DoESLiverpool/st-johns-beacon/large-multi-piece/RCT - Top Windows.stl

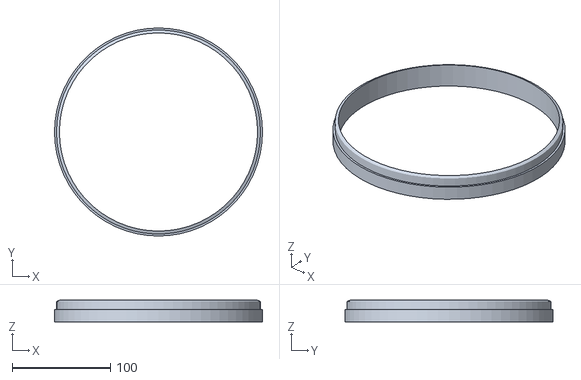
[picture p15: CAD file, 2015-06-18]
large-multi-piece/RCT - Top Windows.stl
211.2 x 211.2 x 22.1
