DoESLiverpool/st-johns-beacon/small-five-piece/St John's Beacon, Radio City Tower - Tower Base 1.stl

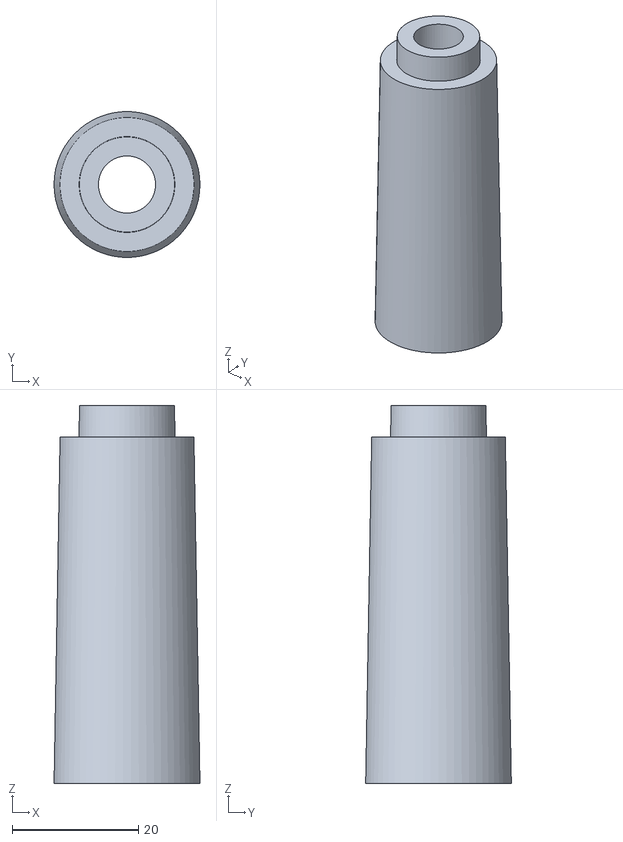
[picture p16: CAD file, 2015-06-10]
small-five-piece/St John's Beacon, Radio City Tower - Tower Base 1.stl
23.2 x 23.1 x 60.0
