DoESLiverpool/st-johns-beacon/large-multi-piece/Letter Ring/letter-i.stl

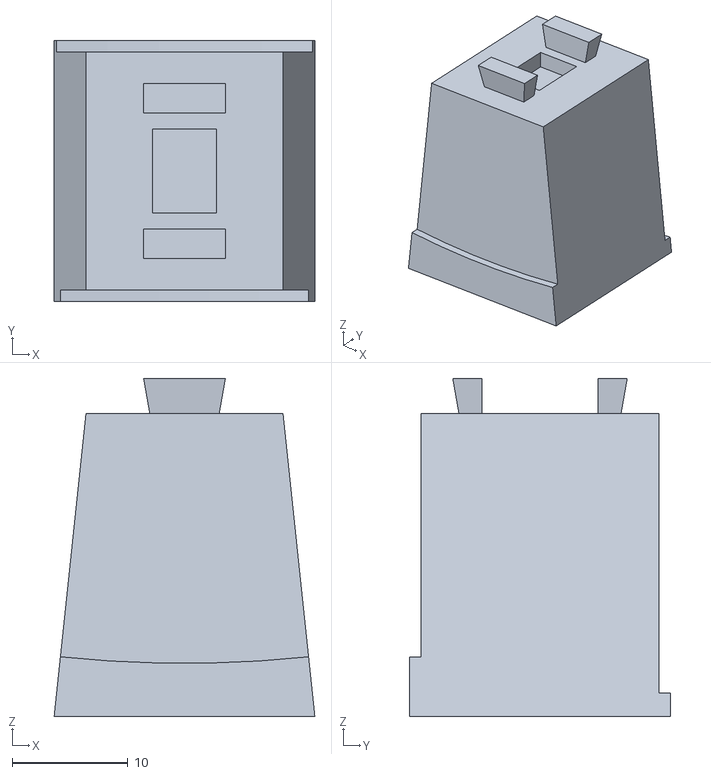
[picture p17: CAD file, 2015-06-19]
large-multi-piece/Letter Ring/letter-i.stl
22.5 x 22.5 x 29.2
