DoESLiverpool/st-johns-beacon/large-multi-piece/RCT - Letter block ring.stl

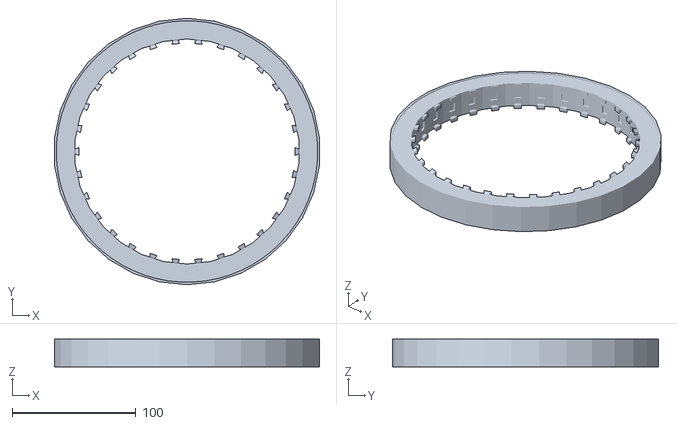
[picture p18: CAD file, 2015-06-18]
large-multi-piece/RCT - Letter block ring.stl
214.1 x 215.3 x 22.5
