DoESLiverpool/st-johns-beacon/small-five-piece/St John's Beacon, Radio City Tower - Tower Base 3.stl

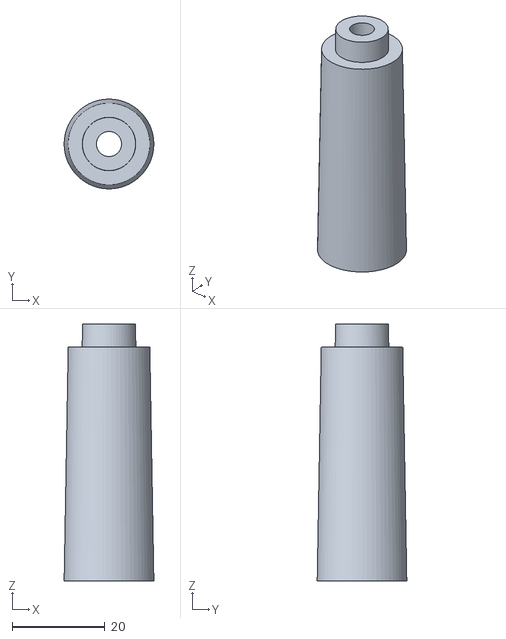
[picture p19: CAD file, 2015-06-10]
small-five-piece/St John's Beacon, Radio City Tower - Tower Base 3.stl
19.3 x 19.3 x 55.3
