DoESLiverpool/st-johns-beacon/large-multi-piece/Letter Ring/letter-S.stl

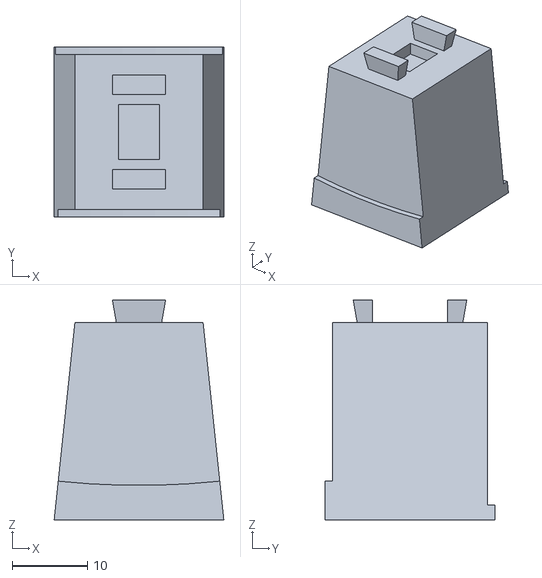
[picture p20: CAD file, 2015-06-19]
large-multi-piece/Letter Ring/letter-S.stl
22.5 x 22.5 x 29.2
