DoESLiverpool/st-johns-beacon/large-multi-piece/RCT - Chimney.stl

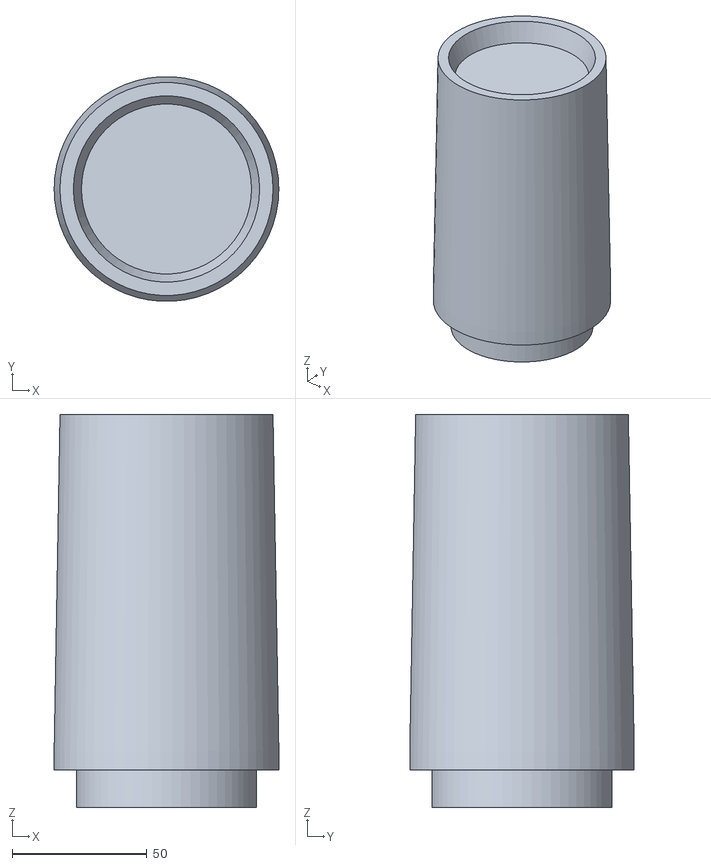
[picture p21: CAD file, 2015-06-15]
large-multi-piece/RCT - Chimney.stl
83.6 x 83.4 x 146.1
