DoESLiverpool/st-johns-beacon/large-multi-piece/RCT - Roof.stl

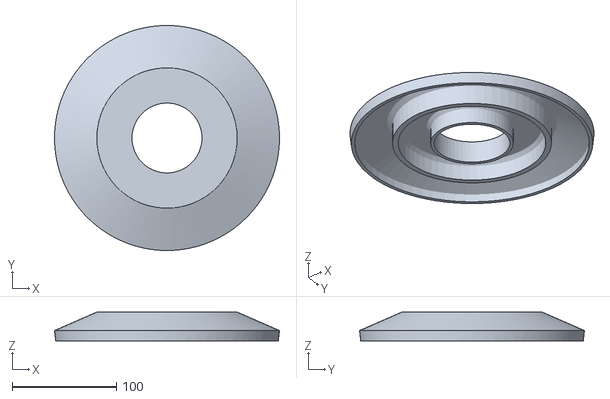
[picture p22: CAD file, 2015-06-15]
large-multi-piece/RCT - Roof.stl
215.5 x 215.4 x 27.6
