DoESLiverpool/st-johns-beacon/large-multi-piece/RCT - Tower Base 2.stl

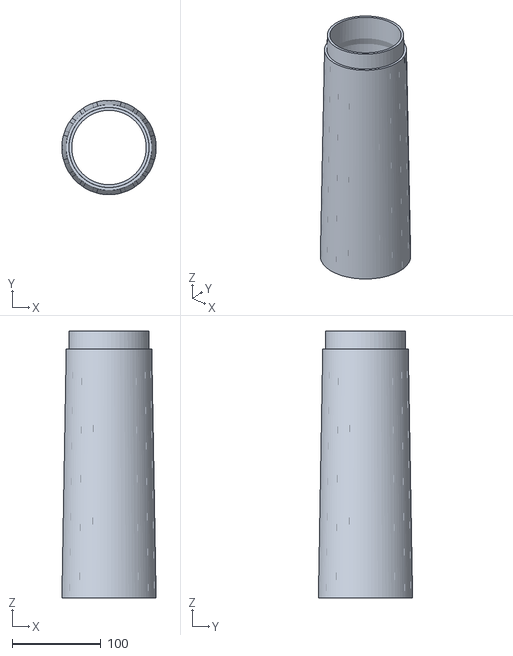
[picture p23: CAD file, 2015-06-15]
large-multi-piece/RCT - Tower Base 2.stl
105.9 x 105.9 x 300.0
