DoESLiverpool/st-johns-beacon/large-multi-piece/RCT - Tower Base 3.stl

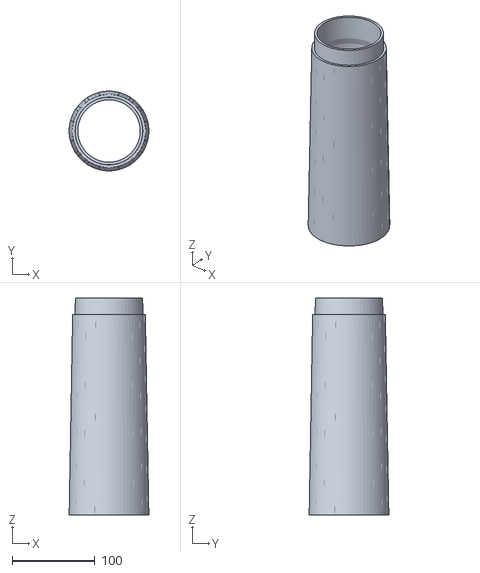
[picture p24: CAD file, 2015-06-15]
large-multi-piece/RCT - Tower Base 3.stl
96.2 x 96.2 x 261.6
